cszielke/ArduDisFace/layout/doc/datasheet/MG12064E.gif

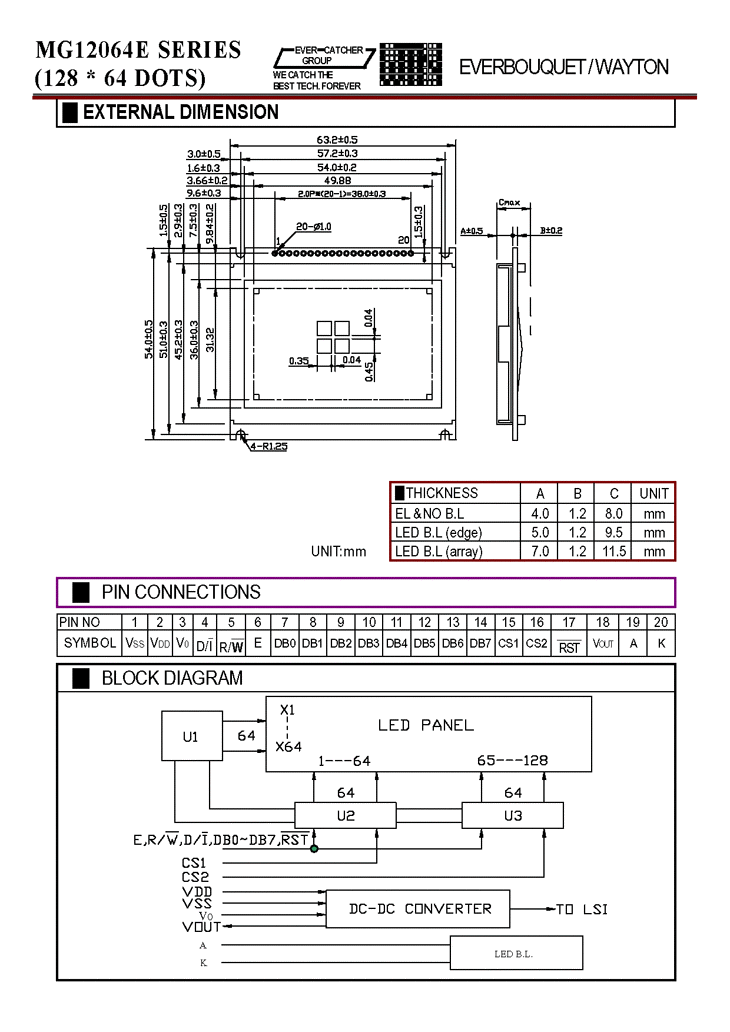
layout/doc/datasheet/MG12064E.gif
