cszielke/ArduDisFace/layout/doc/image/Front-Display.png

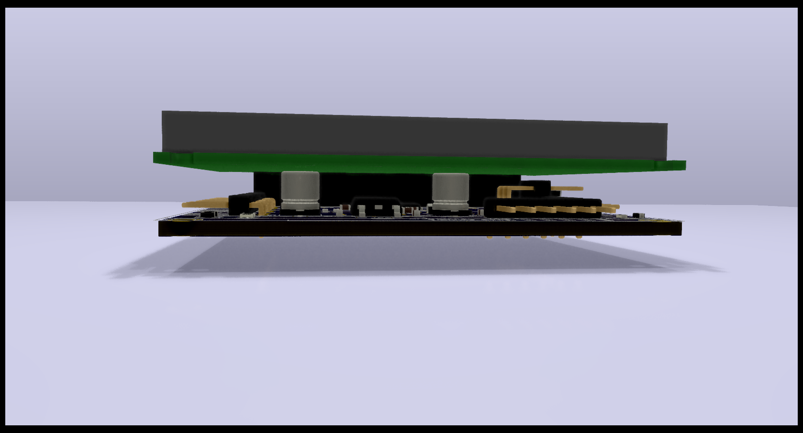
layout/doc/image/Front-Display.png
