cszielke/ArduDisFace/layout/doc/image/Top.png

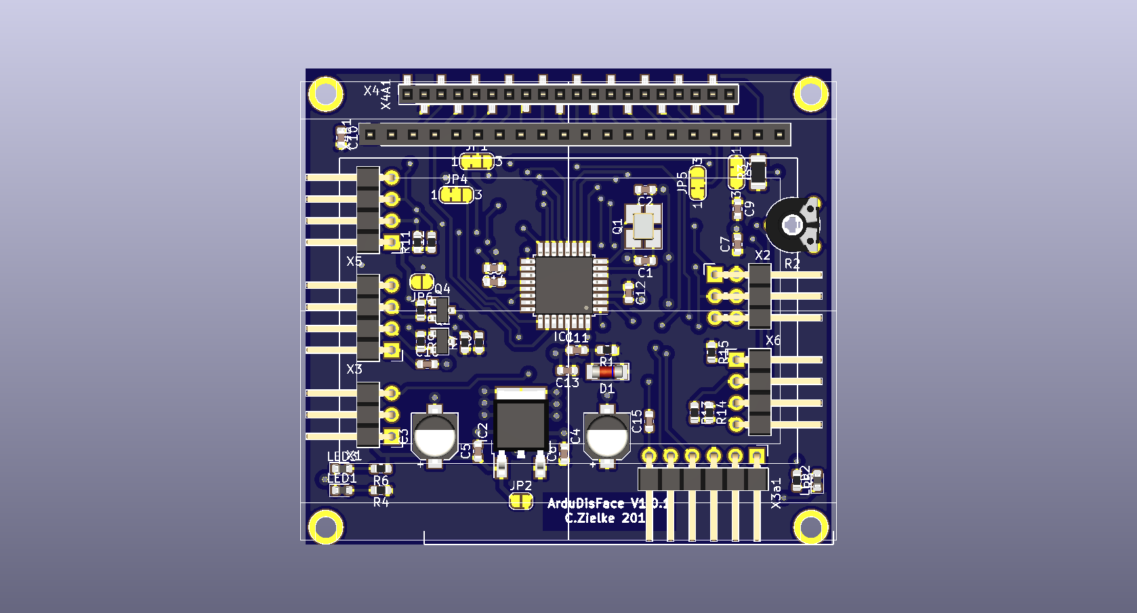
layout/doc/image/Top.png
